eduardocasino/kim-1-programmable-memory-card/firmware/imd.c

/*
 * K-1013 Floppy Disc Controller emulation for the KIM-1 Programmable Memory Board
 *   https://github.com/eduardocasino/kim-1-programmable-memory-card
 *
 * IMD support
 *
 *  Copyright (C) 2024 Eduardo Casino
 *
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
 * You should have received a copy of the GNU General Public License
 * along with this program; if not, write to the Free Software
 * Foundation, Inc., 51 Franklin Street, Fifth Floor, Boston,
 * MA  02110-1301, USA.
 */

#include <stdint.h>
#include <stdbool.h>
#include <stdio.h>
#include <stdlib.h>
#include <string.h>
#include <assert.h>
#include <time.h>

#include "pico/stdlib.h"

#include "ff.h"
#include "f_util.h"

#include "debug.h"
#include "imd.h"
#include "dma.h"
#include "upd765.h"

// File descriptors for FatFs
//
static FATFS fs;
static FIL filpa[MAX_DRIVES];

// Default mounts file
//
static const char * const cfgfile = "mount.cfg";

// Sector sizes
//
static const int sizes[] = { 128, 256, 512, 1024, 2048, 4096, 8192 };

static int imd_check_file_header( FIL *fil )
{
    FRESULT fr;
    uint32_t signature;
    uint8_t c;
    UINT bytes_read = 0;

    debug_printf( DBG_DEBUG, "imd_check_signature()\n" );

    f_rewind( fil );

    if ( FR_OK != ( fr = f_read( fil, &signature, sizeof(signature), &bytes_read ) ) )
    {
        debug_printf( DBG_ERROR, "f_read error: %s (%d)\n", FRESULT_str(fr), fr );
        return -1;
    }

    while ( FR_OK == ( fr = f_read( fil, &c, 1, &bytes_read ) ) )
    {
        if ( c == 0x1A || !bytes_read)
        {
            break;
        }
    }

    if ( FR_OK != fr )
    {
        debug_printf( DBG_ERROR, "f_read error: %s (%d)\n", FRESULT_str(fr), fr );
        return -1;
    }

    if ( 0x1A != c || signature != IMD_SIGNATURE )
    {
        debug_printf( DBG_ERROR, "Bad IMD header\n" );
        return -1;
    }

    return 0;
}

static inline void imd_invalidate_track( imd_track_t *track )
{
    track->imd.data.head = 0xFF;
}

static int imd_get_physical_sector( imd_track_t *track, uint8_t sect )
{
    for ( int nsect = 0; nsect < track->imd.data.sectors; ++nsect )
    {
        if ( sect == track->imd.sector_map[nsect] )
        {
            return nsect;
        }
    }

    return -1;
}

static bool imd_is_compatible_media( imd_track_t *track, bool is_mfm )
{
    return !( ( track->imd.data.mode != 0x00 && track->imd.data.mode != 0x03 )
           || ( track->imd.data.size > 0x03 )
           || ( track->imd.data.mode == 0x00 && is_mfm )
           || ( track->imd.data.mode == 0x03 && !is_mfm ) );
}

static FRESULT f_lseek_read( FIL *fp, FSIZE_t ofs, void *buff, UINT btr, UINT *br )
{
    FRESULT fr;

    fr = f_lseek( fp, ofs );

    if ( FR_OK != fr )
    {
        debug_printf( DBG_ERROR, "f_lseek error: %s (%d)\n", FRESULT_str(fr), fr );
    }
    else
    {
        // Reads sector type + sector data
        fr = f_read( fp, buff, btr, br );

        if ( FR_OK != fr || *br != btr )
        {
            debug_printf( DBG_ERROR, "f_read error: %s (%d)\n", FRESULT_str(fr), fr );
        }
    }

    return fr;
}

static FRESULT f_lseek_write( FIL *fp, FSIZE_t ofs, void *buff, UINT btr, UINT *br )
{
    FRESULT fr;

    fr = f_lseek( fp, ofs );

    if ( FR_OK != fr )
    {
        debug_printf( DBG_ERROR, "f_lseek error: %s (%d)\n", FRESULT_str(fr), fr );
    }
    else
    {
        // Writes sector type + sector data
        fr = f_write( fp, buff, btr, br );

        if ( FR_OK != fr || *br != btr )
        {
            debug_printf( DBG_ERROR, "f_write error: %s (%d)\n", FRESULT_str(fr), fr );
        }
    }

    return fr;
}

// Input are __current__ head and cylinder of the just uncompressed sector
//
static void imd_recalculate_track_map( imd_disk_t *disk, uint8_t head, uint8_t cylinder )
{
    int size_increment = sizes[disk->current_track.imd.data.size] - 1;

    // First, update tracks on the rest of the heads for this cylinder
    for ( uint8_t hd = head+1; hd < disk->heads; ++hd )
    {
        disk->track_map[hd][cylinder] += (uint32_t) size_increment;
    }

    for ( uint8_t cyl = cylinder+1; cyl < disk->cylinders ; ++cyl )
    {
        for ( uint8_t hd = 0; hd < disk->heads; ++hd )
        {
            disk->track_map[hd][cyl] += (uint32_t) size_increment;
        }
    }
}

static void imd_recalculate_track_info( imd_track_t *track, uint8_t sector )
{
    int size_increment = sizes[track->imd.data.size] - 1;

    for ( uint8_t s = sector + 1; s < track->imd.data.sectors; ++s )
    {
        track->imd.sector_info[s].index += (uint32_t) size_increment;
    }
}

static int imd_uncompress_sector( imd_disk_t *disk, uint8_t sector, uint8_t *buffer, int buffer_size )
{
    UINT bytes_read = 0;

    uint32_t idx, init_pos, sector_size, chunk_end, chunk_size, chunk_init, dest_pos;

    debug_printf( DBG_DEBUG, "Uncompressing physical sector %d, cyl %d\n", sector, disk->current_track.imd.data.cylinder );

    assert( !disk->readonly );
    assert( !(disk->current_track.imd.sector_info[sector].type & IMD_TYPE_NORMAL_MASK) );

    idx = disk->current_track.imd.sector_info[sector].index;
    init_pos = idx + 2;
    sector_size = sizes[disk->current_track.imd.data.size];

    chunk_end = (uint32_t)f_size( disk->fil );

    do
    {
        chunk_size = chunk_end - init_pos > (uint32_t)buffer_size ? (uint32_t)buffer_size : chunk_end - init_pos;
        chunk_init = chunk_end - chunk_size > init_pos ? chunk_end - chunk_size : init_pos;
        dest_pos = chunk_init + sector_size - 1;

        if ( FR_OK != f_lseek_read( disk->fil, chunk_init, buffer, chunk_size, &bytes_read ) )
        {
            return -1;
        }

        if ( FR_OK != f_lseek_write( disk->fil, dest_pos, buffer, chunk_size, &bytes_read ) )
        {
            return -1;
        }

        f_sync( disk->fil );

        chunk_end = chunk_init;

    } while ( chunk_init != init_pos );

    if ( FR_OK != f_lseek_read( disk->fil, idx + 1, &buffer[1], 1, &bytes_read ) )
    {
        return -1;
    }

    buffer[0] = disk->current_track.imd.sector_info[sector].type - 1;

    for ( int i = 2; i < (int)sector_size + 1; ++i )
    {
        buffer[i] = buffer[1];
    }

    if ( FR_OK != f_lseek_write( disk->fil, idx, buffer, sector_size + 1, &bytes_read ) )
    {
        return -1;
    }

    f_sync( disk->fil );

    // Recalculate disk track map

    uint8_t cyl  = disk->current_track.imd.data.cylinder;
    uint8_t head = disk->current_track.imd.data.head;

    imd_recalculate_track_map( disk, head, cyl );
    imd_recalculate_track_info( &disk->current_track, sector );

    return 0;
}

// disk->fil must be opened
//
int imd_parse_disk_img( imd_disk_t *disk )
{
    FRESULT fr;
    UINT bytes_read = 0;
    int track;
    uint8_t lastmode = 0, maxhead = 0, maxcyl = 0;

    debug_printf( DBG_DEBUG, "imd_parse_disk_img()\n" );

    assert( disk->fil != NULL );

    // Make sure it is an IMD image file and find the 0x1A mark if returns 0,
    // it is valid an file index is positioned at the beginning of track info
    //
    if ( imd_check_file_header( disk->fil ) )
    {
        return -1;
    }

    for ( track = 0; track < MAX_HEADS * MAX_CYLINDERS_PER_DISK; ++track )
    {
        FSIZE_t track_start = f_tell( disk->fil );

        if ( FR_OK != ( fr = f_read( disk->fil, &disk->current_track.imd, sizeof(imd_data_t), &bytes_read ) ) )
        {
            debug_printf( DBG_ERROR, "f_read error: %s (%d)\n", FRESULT_str(fr), fr );
            return -1;
        }

        if ( 0 == bytes_read )
        {
            // No more tracks
            break;
        }

        debug_printf( DBG_INSANE, "disk->current_track.imd.data.head: %d\n", disk->current_track.imd.data.head );
        debug_printf( DBG_INSANE, "disk->current_track.imd.data.cylinder: %d\n", disk->current_track.imd.data.cylinder );
        debug_printf( DBG_INSANE, "disk->current_track.imd.data.mode: %d\n", disk->current_track.imd.data.mode );
        debug_printf( DBG_INSANE, "disk->current_track.imd.data.sectors: %d\n", disk->current_track.imd.data.sectors );
        debug_printf( DBG_INSANE, "disk->current_track.imd.data.size: %d\n", disk->current_track.imd.data.size );

        bool sect_cyl_map  = disk->current_track.imd.data.head & 0x80;
        bool sect_head_map = disk->current_track.imd.data.head & 0x40;
        uint8_t head_no    = disk->current_track.imd.data.head & 0x3F;

        if ( track != 0 && disk->current_track.imd.data.mode != lastmode )
        {
            debug_printf( DBG_ERROR, "Tracks with different modes not supported\n" );
            return -1;
        }
        lastmode = disk->current_track.imd.data.mode;

        if ( head_no > maxhead ) maxhead = head_no;
        if ( disk->current_track.imd.data.cylinder > maxcyl ) maxcyl = disk->current_track.imd.data.cylinder;

        disk->track_map[head_no][disk->current_track.imd.data.cylinder] = (uint32_t) track_start;

        debug_printf( DBG_INSANE, "track_start: %8.8X\n", disk->track_map[head_no][disk->current_track.imd.data.cylinder] );

        // Skip sector numbering, cylinder and head maps if present
        FSIZE_t ff = f_tell( disk->fil )
            + disk->current_track.imd.data.sectors
                * (1 + (sect_cyl_map ? 1 : 0) + (sect_head_map ? 1 : 0));

        if ( FR_OK != ( fr = f_lseek( disk->fil, ff ) ) )
        {
            debug_printf( DBG_ERROR, "Bad IMD file (truncated?): f_seek error: %s (%d)\n", FRESULT_str(fr), fr );
            return -1;
        }

        // Skip to next track
        for ( int nsect = 0; nsect < disk->current_track.imd.data.sectors; ++nsect )
        {
            uint8_t stype;

            if ( FR_OK != ( fr = f_read( disk->fil, &stype, 1, &bytes_read ) ) )
            {
                debug_printf( DBG_ERROR, "Bad IMD file (truncated?): f_read error: %s (%d)\n", FRESULT_str(fr), fr );
                return -1;
            }

            debug_printf( DBG_INSANE, "  sector: %2.2X, type: %2.2X\n", nsect, stype );

            if ( stype == IMD_UNAVAILABLE )
            {
                debug_printf( DBG_ERROR, "Bad or corrupt file, unsupported sector type: 0x%2.2X\n", stype );
                return -1;
            }

            ff = f_tell( disk->fil );

            if ( stype & IMD_TYPE_NORMAL_MASK )
            {
                // Advance sector size bytes
                ff += sizes[disk->current_track.imd.data.size];
            }
            else
            {
                // Compressed sector, advance 1 byte
                ++ff;
            }

            if ( FR_OK != ( fr = f_lseek( disk->fil, ff ) ) )
            {
                debug_printf( DBG_ERROR, "Bad IMD file (truncated?): f_seek error: %s (%d)\n", FRESULT_str(fr), fr );
                return -1;
            }
        }
    }

    disk->cylinders = maxcyl + 1;
    disk->heads = maxhead + 1;

    return 0;
}

uint8_t imd_seek_track( imd_disk_t *disk, uint8_t head, uint8_t cyl )
{
    UINT bytes_read;
    FRESULT fr;

    debug_printf( DBG_DEBUG, "imd_seek_track(head %2.2X, cyl %2.2X)\n", head, cyl );

    if ( head >= disk->heads || cyl >= disk->cylinders || disk->fil == NULL )
    {
        return 0xFF;
    }

    if ( head == disk->current_track.imd.data.head && cyl == disk->current_track.imd.data.cylinder )
    {
        // Already there
        debug_printf( DBG_DEBUG, "Already there\n" );
        return cyl;
    }

    FSIZE_t idx = disk->track_map[head][cyl];

    debug_printf( DBG_INSANE, "Track index: %8.8X\n", (uint32_t) idx );

    fr = f_lseek( disk->fil, idx );

    if ( FR_OK != fr )
    {
        debug_printf( DBG_ERROR, "f_seek error: %s (%d)\n", FRESULT_str(fr), fr );
        return 0xFF;
    }

    // Load track info

    disk->current_track.track_index = (uint32_t) idx;

    fr = f_read( disk->fil, &disk->current_track.imd.data,
                 sizeof(imd_data_t),
                 &bytes_read );

    if ( FR_OK != fr )
    {
        debug_printf( DBG_ERROR, "f_read error: %s (%d)\n", FRESULT_str(fr), fr );
        return 0xFF;
    }

    bool sect_cyl_map  = disk->current_track.imd.data.head & 0x80;
    bool sect_head_map = disk->current_track.imd.data.head & 0x40;
    disk->current_track.imd.data.head &= 0x3F;

    // Load sector map
    fr = f_read( disk->fil, disk->current_track.imd.sector_map,
                 disk->current_track.imd.data.sectors,
                 &bytes_read );

    if ( FR_OK != fr )
    {
        debug_printf( DBG_ERROR, "f_read error: %s (%d)\n", FRESULT_str(fr), fr );
        return 0xFF;
    }

    // Load sector info (info is in track order, not sector order)
    // First, skip sector cylinder and head maps if present
    idx = f_tell( disk->fil )
        + disk->current_track.imd.data.sectors
            * ((sect_cyl_map ? 1 : 0) + (sect_head_map ? 1 : 0));

    disk->current_track.data_index = (uint32_t) idx;

    if ( FR_OK != f_lseek( disk->fil, idx ) )
    {
        debug_printf( DBG_ERROR, "Bad IMD file (truncated?) SHOULD NOT OCCUR\n" );
        return 0xFF;
    }

    for ( int nsect = 0; nsect < disk->current_track.imd.data.sectors; ++nsect )
    {
        disk->current_track.imd.sector_info[nsect].index = (uint32_t) idx;

        if ( FR_OK != f_read( disk->fil, &disk->current_track.imd.sector_info[nsect].type, 1, &bytes_read ) )
        {
            debug_printf( DBG_ERROR, "Bad imd file (truncated?) SHOULD NOT OCCUR\n" );
            return 0xFF;
        }

        // Calculate and go to next sector index
        idx = f_tell( disk->fil );

        if ( disk->current_track.imd.sector_info[nsect].type & IMD_TYPE_NORMAL_MASK )
        {
            idx += sizes[disk->current_track.imd.data.size];
        }
        else
        {
            ++idx;
        }

        if ( FR_OK != f_lseek( disk->fil, idx ) )
        {
            debug_printf( DBG_ERROR, "Bad IMD file (truncated?) SHOULD NOT OCCUR\n" );
            return 0xFF;
        }
    }

    debug_printf( DBG_DEBUG, "Head %d, Cylinder %d, Track Index %8.8X, Data index %8.8X\n",
        disk->current_track.imd.data.head,
        disk->current_track.imd.data.cylinder,
        disk->current_track.track_index,
        disk->current_track.data_index );

    for ( int nsect = 0; nsect < disk->current_track.imd.data.sectors; ++nsect )
    {
        debug_printf( DBG_INSANE, "-> Sector %2.2d, type %2.2d, index %8.8X\n",
            disk->current_track.imd.sector_map[nsect],
            disk->current_track.imd.sector_info[nsect].type,
            disk->current_track.imd.sector_info[nsect].index );
    }

    return cyl;
}

void imd_read_id( imd_disk_t *disk, bool mf, uint8_t *result )
{
    debug_printf( DBG_DEBUG, "imd_read_id(mf %s)\n", mf ? "true" : "false" );

    if ( !imd_is_compatible_media( &disk->current_track, mf ) )
    {
        result[0] = ST0_ABNORMAL_TERM;
        result[1] = ST1_ND;
        result[2] = 0;
    }
    else
    {
        result[0] = ST0_NORMAL_TERM;
        result[1] = 0;
        result[2] = 0;
        result[3] = disk->current_track.imd.data.cylinder;
        result[4] = disk->current_track.imd.data.head;
        result[5] = disk->current_track.imd.data.sectors;
        result[6] = disk->current_track.imd.data.size;
    }
}

static inline bool imd_skip_sector( bool sk, upd765_data_mode_t mode, uint8_t type, uint8_t *result )
{
    if (   ( mode == NORMAL_DATA  && (type == IMD_NORMAL_DEL || type == IMD_NORMAL_DEL_ERR || type == IMD_COMPRESSED_DEL || type == IMD_COMPRESSED_DEL_ERR) )
        || ( mode == DELETED_DATA && (type == IMD_NORMAL || type == IMD_NORMAL_ERR || type == IMD_COMPRESSED || type == IMD_COMPRESSED_ERR) )
       )
    {
        if ( sk )
        {
            // Skip sector
            return true;
        }
        else
        {
            result[0] |= ST0_ABNORMAL_TERM;
            result[2] |= ST2_CM;
        }
    }
    return false;
}

static int imd_get_nbytes_to_transmit( imd_disk_t *disk, uint8_t nbytes, uint8_t dtl, uint8_t *result )
{
    int trdata = 0;

    if ( disk->current_track.imd.data.size != nbytes )
    {
        if ( nbytes == 0x00 )
        {
            trdata = ( dtl > sizes[disk->current_track.imd.data.size] ) ? sizes[disk->current_track.imd.data.size] : dtl;
        }
        else
        {
            result[0] |= ST0_ABNORMAL_TERM;
            result[1] = ST1_DE;
            result[6] = disk->current_track.imd.data.size;
        }
    }
    else
    {
        trdata = sizes[nbytes];
    }

    return trdata;
}

static int imd_data_cmd_checks( imd_disk_t *disk, uint8_t head, uint8_t cyl, bool mf, uint8_t *result )
{
    if ( head == 1 && disk->heads == 1 )
    {
        result[0] |= ST0_ABNORMAL_TERM | ST0_NOT_READY;
        return -1;
    }

    if ( cyl != disk->current_track.imd.data.cylinder )
    {
        result[0] = ST0_ABNORMAL_TERM;
        result[1] = ST1_ND;
        result[2] = ST2_WC;
        return -1;
    }

    if ( head != disk->current_track.imd.data.head )
    {
        // Update current track with the head info
        //
        if ( cyl != imd_seek_track( disk, head, cyl ) )
        {
            result[0] = ST0_ABNORMAL_TERM | ST0_EC;
            return -1;
        }
    }

    if ( !imd_is_compatible_media( &disk->current_track, mf ) )
    {
        result[0] |= ST0_ABNORMAL_TERM;
        result[1] = ST1_MA;
        return -1;
    }

    return 0;
}

// FIXME: TODO: Support continuing to next track
//
void imd_read_data(
    imd_disk_t *disk,
    uint8_t *buffer,
    bool mt,
    bool mf,
    bool sk,
    uint8_t *result,
    uint8_t head,
    uint8_t cyl,
    uint8_t sect,
    uint8_t nbytes,
    uint8_t eot,
    uint8_t dtl,
    upd765_data_mode_t mode,
    void *dmamem,
    uint16_t max_dma_transfer,
    bool do_copy )
{
    int count = disk->current_track.imd.data.sectors;
    int s;

    debug_printf( DBG_DEBUG, "imd_read_data(mt %s, mf %s, sk %s, "
                                "head %2.2X, cyl %2.2X, sect %2.2X, nbytes %2.2X, eot %2.2X, dtl %2.2X, mode %2.2X\n)",
                            mt ? "true" : "false", mf ? "true" : "false", sk ? "true" : "false",
                            head, cyl, sect, nbytes, eot, dtl, mode );

    // FIXME: Only this is implemented
            // MT -> Multitrack bit                 0 <--- UNIMPLEMENTED
            // MF -> FM (0) / MFM (1) bit           1 <--- IMPLEMENTED
            // SK -> Skip deleted data address mark 0 <--- IMPLEMENTED

    if ( imd_data_cmd_checks( disk, head, cyl, mf, result ) )
    {
        return;
    }

    int trdata = imd_get_nbytes_to_transmit( disk, nbytes, dtl, result );
    if ( trdata == 0 )
    {
        return;
    }

    for ( s = sect; s < count; ++s )
    {
        uint32_t bytes_read = 0;
        UINT br;

        // Get physical sector from interleave table
        int phys = imd_get_physical_sector( &disk->current_track, s );

        debug_printf( DBG_DEBUG, "Reading from cyl %d, soft sector %d, physical sector %d\n", cyl, s, phys );

        if ( phys < 0 )
        {
            debug_printf( DBG_DEBUG, "Sector %d not present in head %d, cyl %d\n", sect, head, cyl );
            result[0] |= ST0_ABNORMAL_TERM;
            result[1] = ST1_ND;
            return;
        }

        result[5] = s;

        imd_sector_t *sector_info = &disk->current_track.imd.sector_info[phys];

        if (   sector_info->type == IMD_NORMAL_DEL_ERR || sector_info->type == IMD_NORMAL_ERR
            || sector_info->type == IMD_COMPRESSED_DEL_ERR || sector_info->type == IMD_COMPRESSED_ERR )
        {
            debug_printf( DBG_DEBUG, "Sector type is %d\n", sector_info->type );
            result[0] |= ST0_ABNORMAL_TERM;
            result[1] |= ST1_DE;
            result[2] |= ST2_DD;
        }

        // Read sector data
        //
        if ( !imd_skip_sector( sk, mode, sector_info->type, result ) )
        {
            int rdsize = sector_info->type & IMD_TYPE_NORMAL_MASK ? sizes[nbytes]+1 : 2;

            if ( FR_OK != f_lseek_read( disk->fil, sector_info->index, buffer, rdsize, &br ) )
            {
                result[0] |= ST0_ABNORMAL_TERM | ST0_EC;
                break;
            }

            debug_printf( DBG_DEBUG,
                            "Read %d bytes from software sector %d, physical sector %d\n",
                            br, s, phys );

            if ( !(sector_info->type & IMD_TYPE_NORMAL_MASK) )
            {
                // Fill the buffer with the repeating byte
                for ( int i = 1; i <= sizes[nbytes]; ++i )
                {
                    buffer[i] = buffer[1];
                }
            }

            // Discard sector type and transfer trdata bytes
            if ( do_copy && (bytes_read + trdata <= max_dma_transfer) )
            {
                dmamem = dma_buffer_to_memory( dmamem, buffer + 1, trdata );
            }

            bytes_read += trdata;

            // Check for bad CRC or DAM errors
            if ( result[0] & ST0_ABNORMAL_TERM )
            {
                // If normal read (not track mode), abort
                break;
            }
        }

        if ( eot == s )
        {
            // Reached EOT
            debug_printf( DBG_DEBUG, "Found EOT, sector %d, soft sector %d\n", s, phys );

            result[0] |= ST0_ABNORMAL_TERM;
            result[1] |= ST1_EN;

            break;
        }
    }

    if ( s == count )
    {
        // EOT sector not found in cylinder
        debug_printf( DBG_DEBUG, "EOT sector not found in cylinder\n" );
        result[0] |= ST0_ABNORMAL_TERM;
        result[1] |= ST1_ND;
    }
}

void imd_write_data(
    imd_disk_t *disk,
    uint8_t *buffer,
    bool mt,
    bool mf,
    bool sk,
    uint8_t *result,
    uint8_t head,
    uint8_t cyl,
    uint8_t sect,
    uint8_t nbytes,
    uint8_t eot,
    uint8_t dtl,
    upd765_data_mode_t mode,
    void *dmamem,
    uint16_t max_dma_transfer,
    bool do_copy )
{
    int count = disk->current_track.imd.data.sectors;
    int s;

    debug_printf( DBG_DEBUG,
                    "imd_write_data(mt %s, mf %s, sk %s, head %2.2X, cyl %2.2X, sect %2.2X, "
                    "nbytes %2.2X, eot %2.2X, dtl %2.2X, mode %2.2X\n)",
                    mt ? "true" : "false", mf ? "true" : "false", sk ? "true" : "false",
                    head, cyl, sect, nbytes, eot, dtl, mode );

    // FIXME: Only this is implemented
            // MT -> Multitrack bit                 0 <--- UNIMPLEMENTED
            // MF -> FM (0) / MFM (1) bit           1 <--- IMPLEMENTED
            // SK -> Skip deleted data address mark 0 <--- IMPLEMENTED

    if ( disk->readonly )
    {
        result[0] = ST0_ABNORMAL_TERM;
        result[1] = ST1_NW;
        return;
    }

    if ( imd_data_cmd_checks( disk, head, cyl, mf, result ) )
    {
        return;
    }

    int trdata = imd_get_nbytes_to_transmit( disk, nbytes, dtl, result );
    if ( trdata == 0 )
    {
        return;
    }

    for ( s = sect; s < count; ++s )
    {
        uint32_t bytes_written = 0;
        UINT bw;

        // Get physical sector from interleave table
        int phys = imd_get_physical_sector( &disk->current_track, s );

        debug_printf( DBG_DEBUG, "Writing to cyl %d, soft sector %d, physical sector %d\n", cyl, s, phys );

        if ( phys < 0 )
        {
            debug_printf( DBG_DEBUG, "Sector %d not present in head %d, cyl %d\n", sect, head, cyl );
            result[0] |= ST0_ABNORMAL_TERM;
            result[1] = ST1_ND;
            return;
        }

        result[5] = s;

        imd_sector_t *sector_info = &disk->current_track.imd.sector_info[phys];

        if ( ( sector_info->type & IMD_TYPE_NORMAL_MASK ) == 0 )
        {
            if ( imd_uncompress_sector( disk, phys, buffer, MAX_SECTOR_SIZE ) )
            {
                debug_printf( DBG_ERROR, "Error uncompressing physical sector %d\n", phys );
                result[0] |= ST0_ABNORMAL_TERM | ST0_EC;
                return;
            }
        }

        // Write sector data
        //
        FRESULT fr = f_lseek( disk->fil, sector_info->index );

        if ( FR_OK != fr )
        {
            debug_printf( DBG_ERROR, "f_seek error: %s (%d)\n", FRESULT_str(fr), fr );
            result[0] |= ST0_ABNORMAL_TERM | ST0_EC;
            break;
        }

        // Put sector type
        buffer[0] = ( mode == NORMAL_DATA ) ? IMD_NORMAL : IMD_NORMAL_DEL;

        if ( do_copy && (bytes_written + trdata <= max_dma_transfer) )
        {
            dmamem = dma_memory_to_buffer( buffer + 1, dmamem, trdata );

            // Writes sector type + sector data
            fr = f_write( disk->fil, buffer, trdata+1, &bw );

            if ( FR_OK != fr || bw != (UINT)(trdata + 1) )
            {
                debug_printf( DBG_ERROR, "f_write error: %s (%d)\n", FRESULT_str(fr), fr );
                result[0] |= ST0_ABNORMAL_TERM | ST0_EC;
                break;
            }
            f_sync( disk->fil );

            // Update sector type in current_track info
            sector_info->type = buffer[0];

            bytes_written += trdata;
        }

        if ( eot == s )
        {
            // Reached EOT
            debug_printf( DBG_INSANE,
                        "Found EOT, sector %d, soft sector %d\n",
                        s, disk->current_track.imd.sector_map[s] );

            result[0] |= ST0_ABNORMAL_TERM;
            result[1] |= ST1_EN;

            break;
        }
    }

    if ( s == count )
    {
        // EOT sector not found in cylinder
        debug_printf( DBG_INSANE, "EOT sector not found in cylinder\n" );
        result[0] |= ST0_ABNORMAL_TERM;
        result[1] |= ST1_ND;
    }
}

void imd_format_track(
    imd_disk_t *disk,
    uint8_t *buffer,
    bool mf,
    uint8_t *result,
    uint8_t head,
    uint8_t nsect,
    uint8_t nbytes,
    uint8_t filler,
    void *dmamem,
    uint16_t max_dma_transfer,
    bool do_copy )
{
    debug_printf( DBG_DEBUG,
                "imd_format_track(head %2.2X, nsect %2.2X, nbytes %2.2X, filler %2.2X)\n",
                head, nsect, nbytes, filler );

    // FIXME: Support multi head

    if ( head == 1 && disk->heads == 1 )
    {
        result[0] |= ST0_ABNORMAL_TERM | ST0_NOT_READY;
        return;
    }

    if ( disk->readonly )
    {
        result[0] = ST0_ABNORMAL_TERM;
        result[1] = ST1_NW;
        return;
    }

    // NOTE: Only supported on already formatted images with the same parameters
    //
    if ( nbytes != disk->current_track.imd.data.size || nsect != disk->current_track.imd.data.sectors )
    {
        result[0] |= ST0_ABNORMAL_TERM;
        result[1] = ST1_MA;
        return;
    }

    uint8_t cyl = disk->current_track.imd.data.cylinder;

    if ( cyl != imd_seek_track( disk, head, cyl ) )
    {
        result[0] |= ST0_ABNORMAL_TERM | ST0_EC;
        return;
    }

    if ( !imd_is_compatible_media( &disk->current_track, mf ) )
    {
        result[0] |= ST0_ABNORMAL_TERM;
        result[1] = ST1_MA;
        return;
    }

    // FIXME: Allow formatting to different sector sizes
    int trdata = sizes[nbytes];

    uint32_t bytes_rw = 0;
    FRESULT fr;
    UINT brw;
    int s;
    for ( s = 0; s < nsect; ++s )
    {
        upd765_format_buf_t format_buf;

        // Copy the format information for the sector
        //
        if ( do_copy && (bytes_rw + sizeof(upd765_format_buf_t) <= max_dma_transfer) )
        {
            dmamem = dma_memory_to_buffer( (uint8_t *)&format_buf, dmamem, sizeof(upd765_format_buf_t) );
        }

        debug_printf( DBG_INSANE,
                        "Formatting physical sector %d, soft sector %d\n",
                        s, format_buf.sect );

        result[5] = format_buf.sect;

        imd_sector_t *sector_info = &disk->current_track.imd.sector_info[s];

        fr = f_lseek( disk->fil, sector_info->index );

        if ( FR_OK != fr )
        {
            debug_printf( DBG_ERROR, "f_seek error: %s (%d)\n", FRESULT_str(fr), fr );
            result[0] |= ST0_ABNORMAL_TERM | ST0_EC;
            break;
        }

        if ( cyl != format_buf.cyl || head != format_buf.head || nbytes != format_buf.nbytes )
        {
            result[0] |= ST0_ABNORMAL_TERM;
            result[1] = ST1_MA;
            break;
        }

        // Update sector map
        //
        disk->current_track.imd.sector_map[s] = format_buf.sect;

        // Fill the buffer with blank data
        //
        int transfer_len;

        if ( sector_info->type & IMD_TYPE_NORMAL_MASK )
        {
            transfer_len = trdata;
            sector_info->type = IMD_NORMAL;
        }
        else
        {
            transfer_len = 1;
            sector_info->type = IMD_COMPRESSED;
        }
        buffer[0] = sector_info->type;

        for ( int i = 1; i <= transfer_len; ++i )
        {
            buffer[i] = filler;        // In case of cmd == FORMAT, this is the filler byte
        }

        // Write sector data to disk
        fr = f_write( disk->fil, buffer, transfer_len+1, &brw );

        if ( FR_OK != fr || brw != (UINT)(transfer_len + 1) )
        {
            debug_printf( DBG_ERROR, "f_write error: %s (%d)\n", FRESULT_str(fr), fr );
            result[0] |= ST0_ABNORMAL_TERM | ST0_EC;
            break;
        }

        bytes_rw += sizeof(upd765_format_buf_t);
    }

    if ( s == nsect )
    {
        // Tried to read/write past last sector in cylinder
        // FIXME: CHECK THIS BEHAVIOUR

        result[1] |= ST1_EN;
    }

    if ( !( result[0] & ST0_ABNORMAL_TERM ) )
    {
        // Write sector map to disk
        //
        fr = f_lseek_write( disk->fil, disk->current_track.track_index + sizeof(imd_data_t),
                                disk->current_track.imd.sector_map, nsect, &brw );

        if ( FR_OK != fr )
        {
            result[0] |= ST0_ABNORMAL_TERM | ST0_EC;
        }

        f_sync( disk->fil );
    }
}

static int imd_write_header( FIL *fp, uint8_t *result, uint8_t *buffer, size_t bufsiz )
{
    static const char header_fmt[] = "IMD 1.18: %s\r\nGenerated by mememul\x1a";
    static const char time_fmt[] = "%d/%m/%y %H:%M:%S";
    time_t now;
    FRESULT fr;
    UINT wcount;

    debug_printf( DBG_DEBUG, "\n" );

    time( &now );

    // Write the time string to buffer[0..off], then format the full header
    // into buffer[off+1..], using buffer (the time string) as the %s argument
    size_t off = strftime( (char *)buffer, bufsiz, time_fmt, localtime( &now ) );
    UINT hsize = (UINT) sprintf( (char *)&buffer[off+1], header_fmt, (char *)buffer );

    debug_printf( DBG_DEBUG, "header: '%s'\n", &buffer[off+1] );

    fr = f_write( fp, &buffer[off+1], hsize, &wcount );

    if ( FR_OK != fr || wcount < hsize )
    {
        debug_printf( DBG_ERROR, "f_write error: %s (%d)\n", FRESULT_str(fr), fr );

        result[0] = ST4_ABNORMAL_TERM;

        if ( FR_OK == fr )
        {
            result[1] = ST5_DISK_FULL;
        }

        return -1;
    }

    return 0;
}

static int imd_write_track_info( FIL *fp, uint8_t *result, imd_data_t *trinfo, uint8_t *smap )
{
    FRESULT fr;
    UINT wcount;

    debug_printf( DBG_DEBUG, "\n" );

    UINT dsize = sizeof( imd_data_t );

    fr = f_write( fp, trinfo, dsize, &wcount );

    if ( FR_OK == fr && wcount == dsize )
    {
        dsize = trinfo->sectors;

        fr = f_write( fp, smap, dsize, &wcount );
    }

    if ( FR_OK != fr || wcount < dsize )
    {
        debug_printf( DBG_ERROR, "f_write error: %s (%d)\n", FRESULT_str(fr), fr );

        result[0] = ST4_ABNORMAL_TERM;

        if ( FR_OK == fr )
        {
            result[1] = ST5_DISK_FULL;
        }

        return -1;
    }

    return 0;
}

static int imd_write_sectors( FIL *fp, uint8_t *result, uint8_t sects, uint8_t *data, size_t size )
{
    FRESULT fr;
    UINT wcount;

    debug_printf( DBG_DEBUG, "sects %d\n", sects );

    for ( uint8_t s = 0; s < sects; ++s )
    {
        fr = f_write( fp, data, size, &wcount );

        if ( FR_OK != fr || wcount < size )
        {
            debug_printf( DBG_ERROR, "f_write error: %s (%d)\n", FRESULT_str(fr), fr );

            result[0] = ST4_ABNORMAL_TERM;

            if ( FR_OK == fr )
            {
                result[1] = ST5_DISK_FULL;
            }

            return -1;
        }
    }

    return 0;
}

void imd_new(
    imd_sd_t *sd,
    uint8_t *result,
    uint8_t *buffer,
    size_t bufsiz,
    char *filename,
    uint8_t heads,
    uint8_t tracks,
    uint8_t sect,
    uint8_t bps,
    uint8_t filler,
    bool packed )
{
    static FIL fp;  // Note: when file descriptors are stack based,
                    // it causes lock-ups when calling from another core
    FRESULT fr;
    imd_data_t trinfo;
    static uint8_t sect_map[255];

    debug_printf( DBG_INFO,
                "filename '%s', tracks %d, sects %d, bps %d, filler 0x%2.2x, packed %d\n",
                filename, tracks, sect, bps, filler, packed );

    result[0] = ST4_NORMAL_TERM;
    result[1] = 0;

    if ( bps >= (uint8_t)(sizeof(sizes) / sizeof(sizes[0])) || sect == 0 )
    {
        result[0] = ST4_ABNORMAL_TERM | ST4_BAD_PARAM;
        return;
    }

    fr = f_open( &fp, filename, FA_WRITE | FA_CREATE_NEW );
    if ( fr != FR_OK )
    {
        debug_printf( DBG_ERROR, "f_open error: %s (%d)\n", FRESULT_str(fr), fr );

        result[0] = ST4_ABNORMAL_TERM;

        if ( FR_EXIST == fr )
        {
            result[1] = ST5_IMG_EXISTS;
        }
        if ( FR_INVALID_NAME == fr )
        {
            result[1] = ST5_IMG_NAME;
        }
        return;
    }

    if ( imd_write_header( &fp, result, buffer, bufsiz ) )
    {
        f_close( &fp );
        return;
    }

    // Initialize immutable track values
    // FIXME: Allow supported modes for the controller
    //        Allow different track modes and sectors

    trinfo.mode = 3;                    // 500 kbps MFM
    trinfo.sectors = sect;
    trinfo.size = bps;

    // Initialize a flat sector map and first sector

    for ( uint8_t s = 0; s < sect; ++s )
    {
        sect_map[s] = s;
    }

    size_t sectsiz;
    if ( packed )
    {
        buffer[0] = 0x02;               // Packed data
        buffer[1] = filler;             // Filler byte
        sectsiz = 2;
    }
    else
    {
        buffer[0] = 0x01;               // Normal data
        for ( int b = 1; b < sizes[bps]+1; ++b )
        {
            buffer[b] = filler;
        }
        sectsiz = sizes[bps]+1;
    }

    for ( int cyl = 0; cyl < tracks; ++cyl )
    {
        for ( int head = 0; head < heads; ++head )
        {
            trinfo.cylinder = cyl;
            trinfo.head = head;

            if ( imd_write_track_info( &fp, result, &trinfo, sect_map ) )
            {
                break;
            }

            if ( imd_write_sectors( &fp, result, trinfo.sectors, buffer, sectsiz ) )
            {
                break;
            }
        }
    }

    f_close( &fp );
}

void imd_image_copy( imd_sd_t *sd, uint8_t *result, uint8_t *buffer, size_t bufsiz, char *source, char *dest, bool owrite )
{
    FRESULT fr;
    static FIL fp_source, fp_dest;  // Note: when file descriptors are stack based,
                                    // it causes lock-ups when calling from another core
    UINT rcount, wcount;

    debug_printf( DBG_INFO, "source '%s', dest '%s'\n", source, dest );

    result[0] = ST4_NORMAL_TERM;
    result[1] = 0;

    if ( !strcmp( source, dest ) )
    {
        debug_printf( DBG_INFO, "Can't copy, source and dest are the same\n" );
        result[0] = ST4_ABNORMAL_TERM;
        result[1] = ST5_IMG_EXISTS;
        return;
    }

    if ( imd_disk_is_image_mounted( sd, dest ) )
    {
        debug_printf( DBG_INFO, "Can't copy, dest image is mounted\n" );
        result[0] = ST4_ABNORMAL_TERM;
        result[1] = ST5_IMG2_MOUNTED;
        return;
    }

    fr = f_open( &fp_source, source, FA_OPEN_EXISTING | FA_READ );
    if ( fr != FR_OK )
    {
        result[0] = ST4_ABNORMAL_TERM;

        if ( FR_NO_FILE == fr || FR_NO_PATH == fr )
        {
            result[0] |= ST4_NOT_FOUND;
        }
        if ( FR_INVALID_NAME == fr )
        {
            result[1] = ST5_IMG_NAME;
        }
        return;
    }

    BYTE wmode = FA_WRITE | (owrite ? FA_CREATE_ALWAYS : FA_CREATE_NEW);

    fr = f_open( &fp_dest, dest, wmode );
    if ( fr != FR_OK )
    {
        f_close( &fp_source );

        result[0] = ST4_ABNORMAL_TERM;

        if ( FR_EXIST == fr )
        {
            result[1] = ST5_IMG_EXISTS;
        }
        if ( FR_INVALID_NAME == fr )
        {
            result[1] = ST5_IMG_NAME;
        }
        return;
    }

    while ( FR_OK == ( fr = f_read( &fp_source, buffer, bufsiz, &rcount ) ) )
    {
        if ( rcount )
        {
            fr = f_write( &fp_dest, buffer, rcount, &wcount );

            if ( FR_OK != fr || wcount < rcount )
            {
                f_close( &fp_source );
                f_close( &fp_dest );

                result[0] = ST4_ABNORMAL_TERM;

                if ( FR_OK == fr )
                {
                    result[1] = ST5_DISK_FULL;
                }
                return;
            }
        }
        if ( rcount < bufsiz )
        {
            break;
        }
    }

    f_close( &fp_source );
    f_close( &fp_dest );

    if ( fr != FR_OK )
    {
        result[0] = ST4_ABNORMAL_TERM;
    }
}

void imd_image_rename( imd_sd_t *sd, uint8_t *result, char *source, char *dest )
{
    FRESULT fr;

    debug_printf( DBG_INFO, "source '%s', dest '%s'\n", source, dest );

    result[0] = ST4_NORMAL_TERM;
    result[1] = 0;

    if ( !strcmp( source, dest ) )
    {
        debug_printf( DBG_INFO, "Can't rename, source and dest are the same\n" );
        result[0] = ST4_ABNORMAL_TERM;
        result[1] = ST5_IMG_EXISTS;
        return;
    }

    if ( imd_disk_is_image_mounted( sd, source ) )
    {
        debug_printf( DBG_INFO, "Can't rename, source image is mounted\n" );
        result[0] = ST4_ABNORMAL_TERM;
        result[1] = ST5_IMG_MOUNTED;
        return;
    }

    if ( imd_disk_is_image_mounted( sd, dest ) )
    {
        debug_printf( DBG_INFO, "Can't rename, dest image is mounted\n" );
        result[0] = ST4_ABNORMAL_TERM;
        result[1] = ST5_IMG2_MOUNTED;
        return;
    }

    fr = f_rename( source, dest );

    if ( fr != FR_OK )
    {
        result[0] = ST4_ABNORMAL_TERM;

        if ( FR_NO_FILE == fr || FR_NO_PATH == fr )
        {
            result[0] |= ST4_NOT_FOUND;
        }
        if ( FR_INVALID_NAME == fr )
        {
            result[1] = ST5_IMG_NAME;
        }
        if ( FR_EXIST == fr )
        {
            result[1] = ST5_IMG_EXISTS;
        }
    }
}

void imd_image_erase( imd_sd_t *sd, uint8_t *result, char *imagename )
{
    FRESULT fr;

    debug_printf( DBG_INFO, "imagename '%s'\n", imagename );

    result[0] = ST4_NORMAL_TERM;
    result[1] = 0;

    if ( imd_disk_is_image_mounted( sd, imagename ) )
    {
        debug_printf( DBG_INFO, "Can't delete, image is mounted\n" );
        result[0] = ST4_ABNORMAL_TERM;
        result[1] = ST5_IMG_MOUNTED;
        return;
    }

    fr = f_unlink( imagename );

    if ( fr != FR_OK )
    {
        result[0] = ST4_ABNORMAL_TERM;

        if ( FR_NO_FILE == fr || FR_NO_PATH == fr )
        {
            result[0] |= ST4_NOT_FOUND;
        }
        if ( FR_INVALID_NAME == fr )
        {
            result[1] = ST5_IMG_NAME;
        }
    }
}

// FIXME: Remove the use of global vars

void imd_disk_mount( imd_sd_t *sd, int fdd_no, uint8_t *result, char *imagename, bool ro )
{
    FRESULT fr;

    debug_printf( DBG_INFO, "fdd %d, imagename '%s', ro %d\n", fdd_no, imagename, ro );

    imd_disk_t *disk = &sd->disks[fdd_no];
    FIL *filp = &filpa[fdd_no];

    if ( result )
    {
        result[0] = ST4_NORMAL_TERM;
        result[1] = 0;
    }

    if ( imd_disk_is_image_mounted( sd, imagename ) )
    {
        // Image already mounted
        debug_printf( DBG_INFO, "Skipping, image already mounted\n" );
        if ( result )
        {
            result[0] = ST4_ABNORMAL_TERM;
            result[1] = ST5_IMG_MOUNTED;
        }
        return;
    }

    if ( imd_disk_is_drive_mounted( sd, fdd_no ) )
    {
        // Drive already mounted
        debug_printf( DBG_INFO, "Skipping, drive already mounted\n" );
        if ( result )
        {
            result[0] = ST4_ABNORMAL_TERM;
            result[1] = ST5_DRV_MOUNTED;
        }
        return;
    }

    if ( imagename[0] == '\0' || strlen( imagename ) > MAX_FILE_NAME_LEN )
    {
        debug_printf( DBG_INFO, "Invalid image name\n" );
        if ( result )
        {
            result[0] = ST4_ABNORMAL_TERM | ST4_NOT_FOUND;
        }
        return;
    }

    // Invalidate current track info so imd_seek_track() does not get confused
    imd_invalidate_track( &disk->current_track );

    while ( true )
    {
        fr = f_open( filp, imagename, FA_READ | FA_WRITE | FA_OPEN_EXISTING );

        if ( FR_OK == fr )
        {
            strcpy( disk->imagename, imagename );
            disk->fil = filp;
            disk->readonly = ro;
            disk->status = ro ? (disk->status | ST3_WP) : (disk->status & ~ST3_WP);

            if ( !imd_parse_disk_img( disk ) )
            {
                debug_printf( DBG_INFO,
                        "Mounted \"%s\", CYLS: %d, HEADS: %d, RO: %d\n",
                        disk->imagename, disk->cylinders, disk->heads, disk->readonly );
                disk->status &= ~ST3_FT;
                disk->status |= ST3_RY;
                disk->status |= (disk->heads == 2) ? ST3_TS : 0;
            }
            else
            {
                debug_printf( DBG_ERROR, "Invalid image format\n" );

                f_close( filp );
                disk->fil = NULL;
                if ( result )
                {
                    result[0] = ST4_ABNORMAL_TERM;
                    result[1] = ST5_IMG_INVALID;
                }
            }
            break;
        }
        else
        {
            if ( FR_NOT_ENABLED == fr )
            {
                debug_printf( DBG_ERROR, "SD Card is not mounted. Mounting and retrying...\n" );

                if ( imd_mount_sd_card( sd ) )
                {
                    disk->fil = NULL;
                    break;
                }
            }
            else
            {
                debug_printf( DBG_ERROR,
                            "f_open(%s) error: %s (%d)\n",
                            imagename, FRESULT_str( fr ), fr );
                disk->fil = NULL;

                if ( result )
                {
                    result[0] = ST4_ABNORMAL_TERM;

                    if ( FR_NO_FILE == fr || FR_NO_PATH == fr )
                    {
                        result[0] |= ST4_NOT_FOUND;
                    }
                    if ( FR_INVALID_NAME == fr )
                    {
                        result[1] = ST5_IMG_NAME;
                    }
                }

                break;
            }
        }
    }
}

void imd_disk_unmount( imd_sd_t *sd, int fdd_no, uint8_t *result )
{
    result[0] = ST4_NORMAL_TERM;
    result[1] = 0;

    debug_printf( DBG_INFO, "fdd %d\n", fdd_no );

    imd_disk_t *disk = &sd->disks[fdd_no];

    if ( disk->fil == NULL )
    {
        // Already unmounted
        debug_printf( DBG_INFO, "Skipping, already unmounted\n" );
        result[0] = ST4_ABNORMAL_TERM;
        result[1] = ST5_DRV_NOT_MOUNTED;
    }
    else
    {
        FRESULT fr = f_close( disk->fil );
        if ( FR_OK == fr )
        {
            disk->fil = NULL;
            disk->imagename[0] = '\0';
            disk->status &= ~ST3_RY;
            disk->status |= ST3_FT;
        }
        else
        {
            debug_printf( DBG_ERROR,
                            "f_close(%d) error: %s (%d)\n",
                            fdd_no, FRESULT_str( fr ), fr );
            result[0] = ST4_ABNORMAL_TERM;
        }
    }
}

void imd_save_mounts( imd_sd_t *sd, uint8_t *result )
{
    char linebuf[256];
    FIL fp;

    result[0] = ST0_NORMAL_TERM;

    if ( FR_OK != f_open( &fp, cfgfile, FA_WRITE | FA_CREATE_ALWAYS ) )
    {
        result[0] = ST0_ABNORMAL_TERM;
        return;
    }

    for ( unsigned drive = 0; drive < MAX_DRIVES; ++drive )
    {
        if ( imd_disk_is_drive_mounted( sd, drive ) )
        {
            sprintf( linebuf, "%u:%s%s\n", drive,
                            sd->disks[drive].imagename,
                            sd->disks[drive].readonly ? ":r" : "" );

            if ( 0 > f_puts( linebuf, &fp ) )
            {
                result[0] = ST0_ABNORMAL_TERM;
                break;
            }
        }
    }

    f_close( &fp );
}

void imd_mount_defaults( imd_sd_t *sd )
{
    char linebuf[256];
    char imagename[256];
    char ro;
    FIL fp;

    if ( FR_OK != f_open( &fp, cfgfile, FA_READ ) )
    {
        return;
    }

    while ( NULL != f_gets( linebuf, sizeof(linebuf), &fp ) )
    {
        unsigned drive;
        int count = sscanf( linebuf, " %u : %255[^: \n] : %c ", &drive, imagename, &ro );

        bool roflag = ( count == 3 && ( ro == 'r' || ro == 'R' ) );

        if ( count > 1 && drive < MAX_DRIVES )
        {
            imd_disk_mount( sd, drive, NULL, imagename, roflag );
        }
    }

    f_close( &fp );
}

void imd_init_dir_listing( imd_sd_t *sd, uint8_t *result )
{
    debug_printf( DBG_DEBUG, "\n" );

    // Close any active dir listing

    if ( sd->dir.is_open )
    {
        f_closedir( &sd->dir.dir );
        sd->dir.is_open = false;
    }

    if ( FR_OK == f_opendir( &sd->dir.dir, "/" ) )
    {
        result[0] = ST4_NORMAL_TERM;
        sd->dir.is_open = true;
    }
    else
    {
        result[0] = ST4_ABNORMAL_TERM;
    }
}

void imd_next_dir_entry( imd_sd_t *sd, uint8_t *result, void *dmamem )
{
    FILINFO fno;

    debug_printf( DBG_DEBUG, "\n" );

    result[0] = ST4_ABNORMAL_TERM;

    if ( !sd->dir.is_open )
    {
        result[0] |= ST4_NOT_OPEN;
    }
    else
    {
        do {
            if ( FR_OK == f_readdir( &sd->dir.dir, &fno ) )
            {
                result[0] = ST4_NORMAL_TERM;

                dma_buffer_to_memory( dmamem, fno.fname, strlen(fno.fname)+1 );

                if ( !fno.fname[0] )
                {
                    f_closedir( &sd->dir.dir );
                    sd->dir.is_open = false;
                    result[0] |= ST4_NO_DATA;
                    break;
                }
            }
            else
            {
                break;
            }
        } while ( fno.fattrib & (AM_HID | AM_SYS | AM_DIR) );
    }
}

// FIXME: Consider that the SD card may not be inserted at this time
//
int imd_mount_sd_card( imd_sd_t *sd )
{
    FRESULT fr = f_mount( &fs, "", 1 );

    if ( FR_OK != fr )
    {
        debug_printf( DBG_ERROR, "f_mount error: %s (%d)\n", FRESULT_str( fr ), fr );
        sd->fs = NULL;
        return -1;
    }

    sd->fs = &fs;
    sd->dir.is_open = false;

    return 0;
}

bool imd_disk_is_drive_mounted( imd_sd_t *sd, int fdd_no )
{
    return ( fdd_no < MAX_DRIVES && sd->disks[fdd_no].fil != NULL );
}

bool imd_disk_is_image_mounted( imd_sd_t *sd, char *imagename )
{
    int d;

    for ( d = 0; d < MAX_DRIVES; ++d )
    {
        if ( sd->disks[d].fil && !strcasecmp( imagename, sd->disks[d].imagename ) )
        {
            break;
        }
    }

    return ( d < MAX_DRIVES );
}

char *imd_disk_get_imagename( imd_sd_t *sd, int fdd_no )
{
    return sd->disks[fdd_no].imagename;
}

bool imd_disk_is_ro( imd_sd_t *sd, int fdd_no )
{
    return sd->disks[fdd_no].readonly;
}
