eduardocasino/kim-1-programmable-memory-card/firmware/picowi/picowi_web.c

// PicoWi Web interface, see http://iosoft.blog/picowi for details
//
// Copyright (c) 2022, Jeremy P Bentham
//
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
// 18/05/2024 - Eduardo Casino - Add support for POST/PUT/PATCH HTTP methods and
//                               some HTTP error support functions
// 19/07/2025 - Eduardo Casino - Add support for DELETE HTTP method and more
//                               HTTP error support functions

#include <stdio.h>
#include <string.h>
#include "picowi_defs.h"
#include "picowi_ip.h"
#include "picowi_net.h"
#include "picowi_tcp.h"
#include "picowi_web.h"

int num_web_handlers;
extern NET_SOCKET net_sockets[NUM_NET_SOCKETS];
WEB_HANDLER web_handlers[MAX_WEB_HANDLERS];

static WEB_METHOD web_methods[] = {
    { HTTP_GET,         "GET " },
    { HTTP_POST,        "POST " },
    { HTTP_PUT,         "PUT " },
    { HTTP_PATCH,       "PATCH " },
    { HTTP_DELETE,      "DELETE " },
    { HTTP_UNSUPPORTED, "" }
};

// Set up a Web page handler
int web_page_handler(web_method_t method, char *uri, web_handler_t handler)
{
    if (num_web_handlers < MAX_WEB_HANDLERS)
    {
        web_handlers[num_web_handlers].method = method;
        web_handlers[num_web_handlers].uri = uri;
        web_handlers[num_web_handlers++].handler = handler;
        return (1);
    }
    return (0);
}    

// Handle a Web page request, return length of response
int web_page_rx(int sock, char *req, int len)
{
    static int lastseq = -1;
    int i, n, found = 0;
    WEB_METHOD *wm=web_methods;
    WEB_HANDLER *whp=web_handlers;
    NET_SOCKET *ts = &net_sockets[sock];
    web_method_t method;
    char *uri;

    if ( lastseq == ts->seq )
    {
        return (ts->web_handler(sock, req, len));
    }
    
    lastseq = ts->seq;

    uri = strchr(req, '/' );

    /* Find method of request*/
    for (; wm->method != HTTP_UNSUPPORTED; wm++)
    {
        n = strlen(wm->method_str);
        if (!memcmp(wm->method_str, req, n))
        {
            break;
        }
    }
    method = wm->method;

    if (method == HTTP_UNSUPPORTED)
    {
        return web_405_method_not_allowed(sock);        
    }

    for (i = 0; i < MAX_WEB_HANDLERS; i++, whp++)
    {
        if (whp->uri && whp->handler)
        {
            n = strlen(whp->uri);
            if (!memcmp(whp->uri, uri, n))
            {
                ++found;
                if (whp->method == method)
                {
                    ts->web_handler = whp->handler;
                    return (whp->handler(sock, req, len));
                }
            }
        }
    }

    if (found)
        return (web_405_method_not_allowed(sock));
    else
        return (web_404_not_found(sock));
}

// Add data to an HTTP response
int web_resp_add_data(int sock, BYTE *data, int dlen)
{
    return (tcp_sock_add_tx_data(sock, data, dlen));
}

// Add string to an HTTP response
int web_resp_add_str(int sock, char *str)
{
    return (tcp_sock_add_tx_data(sock, (BYTE *)str, strlen(str)));
}

// Add content length string to an HTTP response
int web_resp_add_content_len(int sock, int n)
{
    NET_SOCKET *ts = &net_sockets[sock];
    int i = sprintf((char *)&ts->txbuff[TCP_DATA_OFFSET + ts->txdlen], HTTP_CONTENT_LENGTH, n);
    ts->txdlen += i;
    return (i);
}

// Send a Web response
int web_resp_send(int sock)
{
    NET_SOCKET *ts = net_socket_ptr(sock);

    return(tcp_sock_send(sock, TCP_ACK, 0, ts->txdlen));
}

// Send a "204 No Content" response
int web_204_no_content(int sock)
{
    int n;

    n = web_resp_add_str(sock, HTTP_204_OK HTTP_SERVER HTTP_NOCACHE);
    n += web_resp_add_content_len(sock, 0);
    n += web_resp_add_str(sock, HTTP_CONNECTION_CLOSE HTTP_HEADER_END);
    tcp_sock_close(sock);

    return (n);
}

// Send a "400 Bad Request" response
int web_400_bad_request(int sock)
{
    int n;
    
    n = web_resp_add_str(sock, HTTP_400_FAIL HTTP_SERVER HTTP_NOCACHE); 
    n += web_resp_add_content_len(sock, 0);
    n += web_resp_add_str(sock, HTTP_CONNECTION_CLOSE HTTP_HEADER_END);
    tcp_sock_close(sock);
    
    return (n);
}

// Send a "404 Not Found" response
int web_404_not_found(int sock)
{
    int n;
    
    n = web_resp_add_str(sock, HTTP_404_FAIL HTTP_SERVER HTTP_NOCACHE);
    n += web_resp_add_content_len(sock, 0);
    n += web_resp_add_str(sock, HTTP_CONNECTION_CLOSE HTTP_HEADER_END);
    tcp_sock_close(sock);
    
    return (n);
}

// Send a "405 Method Not Allowed" response
int web_405_method_not_allowed(int sock)
{
    int n;

    n = web_resp_add_str(sock, HTTP_405_FAIL HTTP_SERVER HTTP_NOCACHE);
    n += web_resp_add_content_len(sock, 0);
    n += web_resp_add_str(sock, HTTP_CONNECTION_CLOSE HTTP_HEADER_END);
    tcp_sock_close(sock);
    
    return (n);
}

// Send a "409 Conflict" response
int web_409_conflict(int sock, char *reason)
{
    int n;

    n = web_resp_add_str(sock, HTTP_409_FAIL HTTP_SERVER HTTP_NOCACHE HTTP_CONTENT_TEXT);
    n += web_resp_add_content_len(sock, strlen(reason));
    n += web_resp_add_str(sock, HTTP_CONNECTION_CLOSE HTTP_HEADER_END);
    n += web_resp_add_str(sock, reason);

    tcp_sock_close(sock);

    return (n);
}

// Send a "499 Invalid Image Format" response
int web_499_invalid_image_format(int sock)
{
    int n;

    n = web_resp_add_str(sock, HTTP_499_FAIL HTTP_SERVER HTTP_NOCACHE);
    n += web_resp_add_content_len(sock, 0);
    n += web_resp_add_str(sock, HTTP_CONNECTION_CLOSE HTTP_HEADER_END);
    tcp_sock_close(sock);

    return (n);
}

// Send a "500 Internal Server Error" response
int web_500_internal_server_error(int sock)
{
    int n;

    n = web_resp_add_str(sock, HTTP_500_FAIL HTTP_SERVER HTTP_NOCACHE);
    n += web_resp_add_content_len(sock, 0);
    n += web_resp_add_str(sock, HTTP_CONNECTION_CLOSE HTTP_HEADER_END);
    tcp_sock_close(sock);

    return (n);
}

// Send a "507 Insufficient Storage" response
int web_507_insufficient_storage(int sock)
{
    int n;

    n = web_resp_add_str(sock, HTTP_507_FAIL HTTP_SERVER HTTP_NOCACHE);
    n += web_resp_add_content_len(sock, 0);
    n += web_resp_add_str(sock, HTTP_CONNECTION_CLOSE HTTP_HEADER_END);
    tcp_sock_close(sock);

    return (n);
}

// EOF
