eduardocasino/kim-1-programmable-memory-card/firmware/picowi/picowi.h

#ifndef PICOWI_H
#define PICOWI_H

#include "picowi_defs.h"
#include "picowi_pico.h"
#include "picowi_wifi.h"
#include "picowi_init.h"
#include "picowi_ioctl.h"
#include "picowi_event.h"
#include "picowi_join.h"
#include "picowi_ip.h"
#include "picowi_dhcp.h"
#include "picowi_net.h"
#include "picowi_tcp.h"
#include "picowi_web.h"

#endif /* PICOWI_H */
