eduardocasino/kim-1-programmable-memory-card/firmware/picowi/picowi_net.c

// PicoWi net socket interface, see https://iosoft.blog/picowi
//
// Copyright (c) 2022, Jeremy P Bentham
//
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
// 18/05/2024 - Eduardo Casino - Configure country code

#include <stdio.h>
#include <string.h>

#include "picowi_defs.h"
#include "picowi_pico.h"
#include "picowi_wifi.h"
#include "picowi_init.h"
#include "picowi_ioctl.h"
#include "picowi_event.h"
#include "picowi_join.h"
#include "picowi_ip.h"
#include "picowi_net.h"
#include "picowi_udp.h"
#include "picowi_dhcp.h"
#include "picowi_tcp.h"

#define EVENT_POLL_USEC     100000

extern int display_mode;
NET_SOCKET net_sockets[NUM_NET_SOCKETS];
extern int accept_socket;

// Initialise the network stack
int net_init(void)
{
    int ok = 0;
    
    add_event_handler(join_event_handler);
    add_event_handler(arp_event_handler);
    add_event_handler(dhcp_event_handler);
    add_event_handler(udp_event_handler);
    printf("PicoWi DHCP client\n");
    if (!wifi_setup())
        printf("Error: SPI communication\n");
    else if (!wifi_init())
        printf("Error: can't initialise WiFi\n");
    else
        ok = 1;
    return (ok);
}

// Join a network
int net_join(uint32_t country, char *ssid, char *passwd)
{
    int ok = 0;
    
    if (!join_start(country, ssid, passwd))
        printf("Error: can't start network join\n");
    else if (!ip_init(0))
        printf("Error: can't start IP stack\n");
    else
        ok = 1;
    return (ok);
}

// Poll the network interface for events
int net_event_poll(void)
{
    static uint32_t poll_ticks;
    int ret = 0;

    // Get any events, poll the network-join state machine
    if (wifi_get_irq() || ustimeout(&poll_ticks, EVENT_POLL_USEC))
    {
        ret = event_poll();
        join_state_poll(0, 0);
        ustimeout(&poll_ticks, 0);
    }
    return (ret);
}

// Poll the network interface for change of state
void net_state_poll(void)
{
    if (link_check() > 0)
        dhcp_poll();
    // When DHCP is complete, print IP addresses
    if (dhcp_complete == 1 && (display_mode & DISP_INFO))
    {
        printf("DHCP complete, IP address ");
        print_ip_addr(my_ip);
        printf(" router ");
        print_ip_addr(router_ip);
        printf("\n");
        dhcp_complete = 2;
    }
}

// Set socket option
int setsockopt(int sock, int level, int optname, void *optval, socklen_t optlen)
{
    NET_SOCKET *usp = &net_sockets[sock];
    struct timeval *tvp = optval;
    int ret = -1;
    
    if (sock >= 0 && sock <= NUM_NET_SOCKETS)
    {
        if (optname == SO_RCVTIMEO && optlen == sizeof(struct timeval))
        {
            usp->timeout = tvp->tv_sec * 1000000 + tvp->tv_usec;
            ustimeout(&usp->ticks, 0);
            ret = 0;
        }
    }
    return (ret);
}

// Convert IP address to string
char *inet_ntoa(struct in_addr  addr)
{
    static char temps[20];
    unsigned char *a = (unsigned char *)&addr;
    sprintf(temps, "%u.%u.%u.%u", a[0], a[1], a[2], a[3]);
    return (temps);
}

// Open a new socket
int socket(int domain, int type, int protocol)
{
    int sock = type==SOCK_DGRAM ? udp_sock_unused() : tcp_sock_unused();
    
    memset(&net_sockets[sock], 0, sizeof(NET_SOCKET));
    net_sockets[sock].sock_type = type;
    return (sock);
}
        
// Bind a UDP socket to a port (to act as server)
int bind(int sock, struct sockaddr *addr, socklen_t addrlen)
{
    struct sockaddr_in *sinp = (struct sockaddr_in *)addr;
    int ok = -1;
    
    if (sock >= 0 && sock < NUM_NET_SOCKETS)
    {
        if (net_sockets[sock].sock_type == SOCK_DGRAM)
            udp_sock_set(sock, 0, zero_ip, 0, htons(sinp->sin_port));
        else
        {
            add_server_event_handler(tcp_server_event_handler, htons(sinp->sin_port));
            tcp_sock_set(sock, 0, zero_ip, 0, htons(sinp->sin_port));
        }
        ok = 1;
    }
    return (ok);
}

// Set TCP server sockets to accept incoming connections
int listen(int sock, int backlog)
{
    NET_SOCKET *tsp = &net_sockets[sock], *nsp;
    
    tcp_new_state(sock, T_LISTEN);
    while (backlog-- > 1 && (sock=tcp_sock_unused())>=0)
    {
        nsp = &net_sockets[sock];
        *nsp++ = *tsp;
    }
    return (sock >= 0);
}

// Return TCP socket number that has received data, -1 if none
int accept(int server_sock, struct sockaddr *addr, socklen_t *addrlen)
{
    struct sockaddr_in *sin = (struct sockaddr_in *)addr;
    NET_SOCKET *ssp;
    
    if (accept_socket >= 0 && accept_socket < NUM_NET_SOCKETS)
    {
        ssp = &net_sockets[accept_socket];
        sin->sin_len = 4;
        sin->sin_port = htons(ssp->rem_port);
        IP_CPY((uint8_t *)&sin->sin_addr, ssp->rem_ip);
    }
    return (accept_socket);
}

// Receive from a UDP datagram, return the data and IP address
int recvfrom(int sock, void *mem, size_t len, int flags, struct sockaddr *from, socklen_t *fromlen)
{
    int dlen = 0;
    struct sockaddr_in *sinp = (struct sockaddr_in *)from;
    NET_SOCKET *usp = &net_sockets[sock];
    
    if (sock < 0 || sock >= NUM_NET_SOCKETS)
        return (0);
    while (usp->rxlen < UDP_DATA_OFFSET && 
        (usp->timeout == 0 || !ustimeout((uint32_t *)&usp->ticks, usp->timeout)))
    {
        net_event_poll();
        net_state_poll();
    }
    if (usp->rxlen >= UDP_DATA_OFFSET)
    {
        IP_CPY((uint8_t *)&sinp->sin_addr, usp->rem_ip);
        dlen = usp->rxlen - UDP_DATA_OFFSET;
        dlen = dlen < len ? dlen : len;
        memcpy(mem, &usp->rxdata[UDP_DATA_OFFSET], dlen);
        usp->rxlen = 0;
    }
    return (dlen);
}

// Send a UDP datagram
int sendto(int sock, void *data, size_t size, int flags, struct sockaddr *to, socklen_t tolen)
{
    NET_SOCKET *usp = &net_sockets[sock];
    
    if (sock >= 0 && sock < NUM_NET_SOCKETS)
        return (udp_tx(usp->rem_mac, usp->rem_ip, usp->rem_port, usp->loc_port, data, size));
    return (0);
}

// Return pointer to net socket structure, given socket number
NET_SOCKET *net_socket_ptr(int sock)
{
    return(&net_sockets[sock]);
}

// EOF
