eduardocasino/kim-1-programmable-memory-card/firmware/picowi/picowi_wifi.c

// PicoWi half-duplex SPI interface, see https://iosoft.blog/picowi
//
// Copyright (c) 2022, Jeremy P Bentham
//
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
// 18/05/2024 - Eduardo Casino - Remove PIO and DMA code

#include <stdio.h>
#include <string.h>

#include <hardware/clocks.h>
#include "picowi_defs.h"
#include "picowi_pico.h"
#include "picowi_init.h"
#include "picowi_regs.h"
#include "picowi_wifi.h"


extern int display_mode;

// Set up the SPI WiFi interface
int wifi_setup(void)
{
    io_set(SD_ON_PIN, IO_OUT, IO_NOPULL);
    io_out(SD_ON_PIN, 0);
    io_set(SD_CS_PIN, IO_OUT, IO_NOPULL);
    io_out(SD_CS_PIN, 1);
    io_set(SD_CLK_PIN, IO_OUT, IO_NOPULL);
    io_out(SD_CLK_PIN, 0);
    io_set(SD_CMD_PIN, IO_OUT, IO_NOPULL);
    io_out(SD_CMD_PIN, 0);
    usdelay(100000);
    io_out(SD_ON_PIN, 1);
    usdelay(50000);
    io_set(SD_CMD_PIN, IO_IN, IO_PULLUP);
    io_set(SD_IRQ_PIN, IO_IN, IO_NOPULL);
    return (wifi_start());
}

// Start up the WiFi interface
int wifi_start(void)
{
    int ok = 0;
    uint32_t val = 0;
    //uint8_t data[20];

    for (int i = 0; i < 4 && !ok; i++)
    {
        usdelay(2000);
        val = wifi_reg_read(SD_FUNC_BUS_SWAP, 0x14, 4);
        ok = (val == SPI_TEST_VALUE);
    }
    if (!ok)
        printf("Error: SPI test pattern %08lX\n", val);
    else
    {
        printf("Detected WiFi chip\n");
        // Rx data changes on rising clock edge (default)
        wifi_reg_write(SD_FUNC_BUS_SWAP, SPI_BUS_CONTROL_REG, 0x200b3, 4);
        // Rx data changes on falling clock edge
        //wifi_reg_write(SD_FUNC_BUS_SWAP, SPI_BUS_CONTROL_REG, 0x200a3, 4);
        val = wifi_reg_read(SD_FUNC_BUS, 0x14, 4);
        ok = (val == SPI_TEST_VALUE);
        if (!ok)
            printf("Error: SPI swap pattern %08lX\n", val);
#if 1
        // Set WiFi chip SPI delay and interrupts
        wifi_reg_read(SD_FUNC_BUS, SPI_BUS_CONTROL_REG, 4);
        wifi_reg_read(SD_FUNC_BUS, SPI_BUS_CONTROL_REG, 4);
        wifi_reg_write(SD_FUNC_BUS, SPI_RESP_DELAY_F1_REG, 0x04, 1);
        wifi_reg_write(SD_FUNC_BUS, SPI_INTERRUPT_REG, 0x0099, 2);
        wifi_reg_write(SD_FUNC_BUS, SPI_INTERRUPT_ENABLE_REG, 0x00be, 2);
#else        
        n = wifi_data_read(SD_FUNC_BUS, 0x14, data, 4);
        disp_bytes(0, data, n);
        printf("\n");
#endif
    }
    return (ok);
}


// Read a register
uint32_t wifi_reg_read(int func, uint32_t addr, int nbytes)
{
    uint32_t val, ret;
    
    wifi_data_read(func, addr, (uint8_t *)&val, nbytes);
    ret = func&SD_FUNC_SWAP && nbytes > 1 ? SWAP16_2(val) : val;
    display(DISP_REG,
        "Rd_reg   len %u %s 0x%04lx -> 0x%02lX\n", 
        nbytes,
        wifi_func_str(func),
        addr&SB_ADDR_MASK,
        ret);
    return (ret);
}

// Write a register
int wifi_reg_write(int func, uint32_t addr, uint32_t val, int nbytes)
{
    int ret;
    
    if (func & SD_FUNC_SWAP && nbytes > 1)
        val = SWAP16_2(val);
    ret = wifi_data_write(func, addr, (uint8_t *)&val, nbytes);
    display(DISP_REG,
        "Wr_reg   len %u %s 0x%04lx <- 0x%02lX\n",
        nbytes,
        wifi_func_str(func),
        addr&SB_ADDR_MASK,
        val);
    return (ret);
}

// Read data block using SPI
int wifi_data_read(int func, int addr, uint8_t *dp, int nbytes)
{
    SPI_MSG msg = {
        .hdr = { 
        .wr = SD_RD,
        .incr = 1,
        .func = func&SD_FUNC_MASK,
        .addr = addr,
        .len = nbytes 
    } 
    };
    U32DATA dat = { .uint32 = 0 };

    io_mode(SD_CMD_PIN, IO_OUT);
    if (func & SD_FUNC_SWAP)
        msg.vals[0] = SWAP16_2(msg.vals[0]);
    else if (func == SD_FUNC_BAK)
        msg.hdr.len += 4;
    else if (func == SD_FUNC_RAD)
        nbytes = (nbytes + 3) & ~3;
    io_out(SD_CS_PIN, 0);
    wifi_spi_write((uint8_t *)&msg, 32);
    io_mode(SD_CMD_PIN, IO_IN);
    if (func == SD_FUNC_BAK)
        wifi_spi_read(dat.bytes, 32);
    dat.uint32 = 0;
    wifi_spi_read(dp, nbytes * 8);
    io_out(SD_CS_PIN, 1);
    return (nbytes);
}

// Write a data block using SPI
int wifi_data_write(int func, int addr, uint8_t *dp, int nbytes)
{
    SPI_MSG msg = {
        .hdr = {
         .wr = SD_WR,
        .incr = 1,
        .func = func&SD_FUNC_MASK,
        .addr = addr,
        .len = nbytes
    }
    };

    if (func & SD_FUNC_SWAP)
        msg.vals[0] = SWAP16_2(msg.vals[0]);
    io_mode(SD_CMD_PIN, IO_OUT);
    io_out(SD_CS_PIN, 0);
    if (nbytes <= 4)
    {
        memcpy(&msg.bytes[4], dp, nbytes);
        wifi_spi_write((uint8_t *)&msg, 64);
    }
    else
    {
        wifi_spi_write((uint8_t *)&msg, 32);
        wifi_spi_write(dp, nbytes * 8);
    }
    io_out(SD_CS_PIN, 1);
    io_mode(SD_CMD_PIN, IO_IN);
    return (nbytes);
}

// Poll for WiFi receive data event, with timeout
bool wifi_rx_event_wait(int msec, uint8_t evt)
{
    bool ok;
    
    while (!(ok = (wifi_reg_read(SD_FUNC_BUS, BUS_SPI_STATUS_REG, 1) & evt) == evt) && msec--)
        usdelay(1000);
    return (ok);
}

// Read data from SPI interface, using bit-bash
int wifi_spi_read(uint8_t *data, int nbits)
{
    uint8_t b, *start = data;
    int n = 0;

    data--;
    while (n < nbits)
    {
        b = IO_RD(SD_DIN_PIN);
        IO_WR_HI(SD_CLK_PIN);
        //b = IO_RD(SD_DIN_PIN);
        if ((n++ & 7) == 0)
            * ++data = 0;        
        *data = (*data << 1) | b;
        IO_WR_LO(SD_CLK_PIN);
    }
    display(DISP_SPI, "Rd_SPI ");
    disp_bytes(DISP_SPI, start, nbits / 8);
    display(DISP_SPI, "\n");
    return (nbits);
}

// Write data to SPI interface, using bit-bash
void wifi_spi_write(uint8_t *data, int nbits)
{
    uint8_t b = 0, *start = data;
    int n = 0;

    io_mode(SD_CMD_PIN, IO_OUT);
    b = *data++;
    while (n < nbits)
    {
        IO_WR(SD_CMD_PIN, b & 0x80);
        IO_WR_HI(SD_CLK_PIN);
        b <<= 1;
        if ((++n & 7) == 0)
            b = *data++;
        IO_WR_LO(SD_CLK_PIN);
    }
    io_mode(SD_CMD_PIN, IO_IN);
    display(DISP_SPI, "Wr_SPI ");
    disp_bytes(DISP_SPI, start, nbits / 8);
    display(DISP_SPI, "\n");
}

// Get state of IRQ pin
bool wifi_get_irq(void)
{
#if SD_IRQ_ASSERT
    return (io_in(SD_IRQ_PIN));
#else
    return (!io_in(SD_IRQ_PIN));
#endif    
}

// Return string with function name
char *wifi_func_str(int func)
{
    func &= SD_FUNC_MASK;
    return (func == SD_FUNC_BUS ? "Bus" :
           func == SD_FUNC_BAK ? "Bak" :
           func == SD_FUNC_RAD ? "Rad" : "???");
}

// EOF
